Leonardboeker/Hardware_III/.planning/PROJECT.md

# Hardware III — Guided Comparative Assembly

**Subtitle:** An interactive construction kitchen — configure, build, compare.
**Proposal submitted:** April 17, 2026 (`Group_3_Hardware_III_Proposal.pdf`)

## What This Is

A hands-on exhibit for children, young architects, and decision makers.
The user configures a building (footprint, height, material) using physical ArUco pucks and dials on a table. A projector guides them through 5 construction phases — each with CO₂, cost, labor, and logistics data. Three construction methods can be compared: Masonry, 3D Printed, Prefab. No screens. No buttons.

## Core Value

Turn abstract construction data into embodied knowledge:
you *build* the comparison yourself, piece by piece — the statistics emerge from your own hands.

## Concept

**Flow per model:**
1. Piece highlight projected → where to place next element
2. User places physical piece → camera/Kinect confirms position
3. Data appears projected on/around the piece: CO₂, labor hours, material origin, method explanation
4. Sound layer reinforces the data (industrial noise, time-lapse audio, factory vs. site sounds)
5. Next piece highlighted → repeat until model complete
6. Model summary shown → move to next construction method model

**After all models complete:**
- Full comparison statistics projected across all models simultaneously
- CO₂ totals, labor hours, time, cost — side by side
- Sound transitions to a final ambient layer

**Construction methods to compare (TBD, 2–4 models):**
- Traditional masonry / site-built
- 3D-printed concrete / robotic extrusion
- Modular prefabrication / CLT
- (Strong candidate) Reclaimed / reused brick — near-zero embodied carbon, outperforms 3DP on every metric, sharpens the political argument

## FSM States (locked in proposal)

```
IDLE → METHOD → FOOTPRINT → HEIGHT → MATERIALS → VALIDATED → 5 PHASES → COMPARISON
```

- **IDLE**: No model on pedestal
- **METHOD**: RFID read → construction method selected (Masonry / 3D Printed / Prefab)
- **FOOTPRINT**: User arranges 10 ArUco pucks → footprint + m² calculated
- **HEIGHT**: User rotates ArUco dial (ID 10) → floors selected
- **MATERIALS**: User rotates ArUco dial (ID 11) → material variant selected
- **VALIDATED**: System checks feasibility (e.g. earth 3DP max 1 story) → green/red feedback
- **5 PHASES**: Foundation → Structure → Roof → Openings → Finishing (animated, data per phase)
- **COMPARISON**: All data saved, side-by-side dashboard projected

## Layered State Model (current runtime interpretation)

The project now distinguishes three state layers:

1. **Canonical Content FSM**
   `IDLE -> METHOD -> FOOTPRINT -> HEIGHT -> MATERIALS -> VALIDATED -> PHASE_N -> COMPARISON`
2. **System Wrapper States**
   `CALIBRATION_CHECK`, `ERROR`, `RESET`, `MANUAL_OVERRIDE`
3. **Visual Feedback States**
   `DISCONNECTED`, `PENDING`, `INVALID`, `VALID`, `IDLE_ANIM`, `SUMMARY`, `COMPARISON`

The current TouchDesigner runtime should keep these layers separate.
The visitor-facing journey is the canonical content FSM.
Recovery and setup belong to wrapper states.
Projection feedback belongs to visual states.

## Building Phases (locked)

| Phase | Name |
|---|---|
| 1 | Foundation |
| 2 | Structure / Walls |
| 3 | Roof |
| 4 | Openings (windows/doors) |
| 5 | Finishing |

## Input / Sensing

- **USB Webcam overhead**: detects piece placement position on table surface
- **Kinect** (optional): depth sensing for better 3D object recognition, height
- **ESP32 + proximity sensor**: detects when user leans in / reaches for piece → triggers data layer zoom
- **Physical pieces**: color-coded or marker-tagged parts per construction method

## Output

- **Projection on table surface + model surfaces**: placement guides, data overlays, statistics
- **Sound**: construction method audio per step (concrete mixer, robotic printer hum, timber assembly)
- **Statistics view**: final comparison projected as graphic across full table

## Toolkit

- **TouchDesigner** — primary runtime (FSM, projection mapping, vision pipeline). Replaces Anemone/Firefly per locked decision (see below).
- **OpenCV + ArUco** (Python or TD Script CHOP) — camera intake + marker detection
- **Rhino + Grasshopper** — parametric geometry, building generation per method (no longer carries the FSM)
- **Arduino / ESP32** — RFID pedestal + proximity sensor; OSC over WiFi to TouchDesigner
- USB webcam overhead + top-down video projector

## Context

**Course:** Hardware III seminar, MRAC + MAAI 2025/2026
**Instructors:** Hamid Peiro, Aleksandra (Sasha) Kraeva
**Schedule:** 5 course days + Finals (April 10 – May 22, 2026)
**User background:** Ausstellungsbau (exhibition design) — content must be critical and substantive, not just visually reactive

**Key theoretical reference:** Stefana Parascho, "Cooperative Robotic Assembly" (ETH Diss. 25839)
— assembly sequence as FSM, each intermediate state must be valid → directly maps to guided piece placement

**Reference projects (from S1 review):**
- Gramazio Kohler, Augmented Bricklaying, ETH 2018–20 — direct precedent for AR-guided assembly
- Fologram, Steampunk Pavilion, Tallinn 2019 — guided assembly proven with public
- MIT Tangible Media, inFORM, 2013 — canonical tangible dataviz reference
- EPFL SXL, Corentin Fivet — reuse + embodied carbon as design driver
- Striatus Bridge (ZHA + BRG + ETH, 2021) — 3DP concrete visual reference
- Domestic Data Streamers — participatory physical dataviz

**White space:** No precedent exists for a tabletop interactive LCA comparison installation combining guided assembly + tangible dataviz + LCA at table scale.

## Constraints

- **Timeline:** S1 proposal due April 17 — concept locked, execution starts
- **Tech Stack:** Rhino + Grasshopper mandatory (course toolkit)
- **Output:** Projection on physical surface — no screens
- **Team:** Group project — PM schedule required from S1
- **Data:** CO₂ and labor hour data must be sourced/researched for each construction method
- **Models:** Physical replica parts must be fabricated (3D print or laser cut) before Session 4

## Key Decisions

| Decision | Rationale | Outcome |
|---|---|---|
| Comparative structure (2–4 models) | Makes data tangible through contrast | — Pending |
| Guided assembly (not free exploration) | Matches course requirement: FSM + human-in-the-loop | — Pending |
| Table projection (top-down) | Easier calibration, direct piece-to-data feedback | — Pending |
| ArUco fiducial markers on pieces | Color detection unreliable under projector light | — Pending (recommended over color) |
| Sound as equal layer to visuals | Ausstellungsbau background — content depth matters | — Pending |
| Runtime: TouchDesigner vs GH/Anemone | GH is single-threaded; Anemone stalls canvas; webcam under projector light is fragile — TD does projection mapping + CV natively | **LOCKED 2026-05-03 — TouchDesigner** (lit-review strand 03) |
| Build all 3 methods physically vs. 1 physical + 2 animated | 3 full builds = visitor fatigue risk | **LOCKED 2026-05-03 — projected animations**, AI-generated animations paused until LCA numbers sourced |
| LCA data as ranges (with sources) vs. single figures | Single EPD figures vary wildly and collapse under expert questioning | **LOCKED 2026-05-03 — ranges + tier-annotated sources** + methodology-wobble overlay as first-class layer |
| Closed-loop CV vs open-loop button-advance | Closed-loop is the project's novelty contribution; open-loop is a v1 baseline | **LOCKED 2026-05-03 — closed-loop from day one**, manual-override hotkey as emergency demo insurance only |
| Reclaimed brick: 4th competitor vs baseline toggle | A reuse-vs-new bake-off is foregone-conclusion theater | **LOCKED 2026-05-03 — baseline toggle**, frames every other method against it |

## Open Critiques (from S1 peer review — address in proposal)

1. Three full builds may exhaust visitors — consider 1 physical + 2 projected animations
2. LCA numbers must be ranges with cited sources, not single figures
3. Labor-hours mapping is symbolic, not embodied — own that framing explicitly
4. Missing political dimension: who loses jobs in each method?
5. Reused/reclaimed brick as a 4th method is the strongest narrative upgrade available

See `.planning/REVIEW-S1.md` for full critique, additions, and references.

---

## Locked decisions (2026-05-03)

These five positions are taken — backed by the literature review at `docs/research/lit-review/`. They supersede any earlier "Open" entries above. Cited rationale lives in `docs/research/lit-review/ACTIONS.md`.

1. **Closed-loop computer vision from day one.** Every FSM transition is gated by camera confirmation against a projected target.
2. **TouchDesigner is the runtime.** Replaces Anemone (FSM) and Firefly (vision intake) from the original toolkit.
3. **Reclaimed brick is a baseline toggle**, not a 4th competitor.
4. **Methodology-wobble is a first-class projection layer**, not a footnote.
5. **AI-generated phase animations paused** until tier-1 LCA numbers are sourced (Catalonia: CYPE / BEDEC / ITeC / EPDs).

---
*Last updated: 2026-05-03 — toolkit + key decisions realigned to lit-review-backed locked positions*
