Leonardboeker/Hardware_III/.planning/phases/02.1-height-slider/02.1-01-firmware-slider-adc-PLAN.md

---
phase: 02.1-height-slider
plan: 01
type: execute
wave: 1
depends_on: []
files_modified:
  - firmware/esp32-rfid/esp32_rfid/esp32_rfid.ino
autonomous: false
requirements:
  - INP-03
must_haves:
  truths:
    - "ESP32 reads slider on GPIO34 every ~50 ms"
    - "Slider value is median-then-EMA smoothed before quantization"
    - "Firmware emits `FLOOR:<int>` on quantized floor change"
    - "Firmware emits `SLIDER:<0.xxx>` periodically (~200 ms) as alive/debug tick"
    - "Floor boundary hysteresis prevents oscillation"
    - "Existing `RFID:` / `HB:` / `BOOT:` line formats and RC522 SPI pins remain unbroken"
  artifacts:
    - path: "firmware/esp32-rfid/esp32_rfid/esp32_rfid.ino"
      provides: "ESP32 RFID + Slider firmware (single sketch)"
      contains: "constexpr uint8_t SLIDER_PIN = 34"
    - path: "firmware/esp32-rfid/esp32_rfid/esp32_rfid.ino"
      provides: "FLOOR/SLIDER Serial emission"
      contains: "Serial.printf"
  key_links:
    - from: "esp32_rfid.ino loop()"
      to: "analogReadMilliVolts(SLIDER_PIN)"
      via: "ADC sample every ~50 ms"
      pattern: "analogReadMilliVolts\\(SLIDER_PIN\\)"
    - from: "esp32_rfid.ino loop()"
      to: "Serial output"
      via: "FLOOR:/SLIDER: printf"
      pattern: "FLOOR:|SLIDER:"
---

<objective>
Extend the existing ESP32-RFID sketch so it ALSO reads a DollaTek 10K linear-slide potentiometer on GPIO34, smooths it (median FIRST, EMA SECOND), quantizes to a floor index with boundary hysteresis, and emits `FLOOR:<int>` (on change) + `SLIDER:<0.xxx>` (periodic) over USB Serial @115200 — alongside the unchanged `RFID:<HEX>`, `HB:<sec>`, `BOOT:rfid_reader_ready` lines.

Purpose: HEIGHT FSM state needs a physical input. The DollaTek slider replaces ArUco-Dial ID-10 (per ROADMAP Phase 02.1 + CONTEXT.md decision D-Hardware). This is the ONLY firmware change in Phase 02.1; nothing else in the sketch (RFID logic, heartbeat cadence, SPI pins) may shift.
Output: A single rewritten `esp32_rfid.ino` that, when flashed and opened in a Serial Monitor @115200, shows the existing `BOOT:` + `HB:N` + (on tag scan) `RFID:<HEX>` lines PLUS new `FLOOR:N` (only when floor changes) and `SLIDER:0.xxx` (every ~200 ms) lines.
</objective>

<execution_context>
@~/.claude/get-shit-done/workflows/execute-plan.md
@~/.claude/get-shit-done/templates/summary.md
</execution_context>

<context>
@.planning/STATE.md
@.planning/ROADMAP.md
@.planning/phases/02.1-height-slider/02.1-CONTEXT.md
@firmware/esp32-rfid/esp32_rfid/esp32_rfid.ino
@firmware/esp32-rfid/README.md

<interfaces>
<!-- Current Serial line shapes that MUST keep working unchanged. -->
<!-- Existing format (from esp32_rfid.ino lines 37, 46-48, 61-62): -->

BOOT:rfid_reader_ready          // one-shot at boot, line 37
HB:<seconds-since-boot>         // every 1000 ms, lines 46-48
RFID:<UPPERCASE-HEX-UID>        // on new tag (debounced REREAD_MS=1500), lines 61-62

<!-- New line shapes this plan introduces: -->

FLOOR:<int>                     // emitted only on quantized floor change, 1..MAX_FLOORS
SLIDER:<0.xxx>                  // emitted every ~200 ms (3 decimals), smoothed normalized value

<!-- Existing pin reservations that MUST NOT collide with SLIDER_PIN=34: -->

SS_PIN  = 5     // RC522 SDA/SS  (line 21)
SCK     = 18    // SPI clock
MOSI    = 23
MISO    = 19
RST_PIN = 27    // RC522 RST     (line 22)

<!-- GPIO34 is input-only on ESP32, ADC1_CH6 (WiFi-safe). Confirmed by CONTEXT.md. -->
</interfaces>
</context>

<tasks>

<task type="auto" tdd="false">
  <name>Task 1: Add slider constants, ring buffer, EMA state, and helper functions at the top of esp32_rfid.ino</name>
  <files>firmware/esp32-rfid/esp32_rfid/esp32_rfid.ino</files>
  <read_first>
    - firmware/esp32-rfid/esp32_rfid/esp32_rfid.ino (current sketch — see existing constexpr block lines 21-22 and the include block lines 18-19)
    - .planning/phases/02.1-height-slider/02.1-CONTEXT.md (locked decisions block — verbatim values below)
  </read_first>
  <action>
    Edit `firmware/esp32-rfid/esp32_rfid/esp32_rfid.ino`.

    1. After line 19 (`#include <MFRC522.h>`), add `#include <algorithm>` so `std::nth_element` is available for the median.

    2. After the existing RC522 constexpr block (currently lines 21-22 `SS_PIN`/`RST_PIN`), add a new constexpr block for the slider — keep grouping tight so wiring/docs match. Insert verbatim:

       ```cpp
       // ---- Slider (DollaTek 10K linear-slide potentiometer) ----
       // GPIO34 is input-only on ESP32, ADC1_CH6, WiFi-safe.
       constexpr uint8_t  SLIDER_PIN          = 34;
       constexpr uint8_t  MAX_FLOORS          = 5;        // upper bound; per-method caps live TD-side
       constexpr uint8_t  MEDIAN_WINDOW       = 8;        // ring buffer size (CONTEXT.md: median FIRST)
       constexpr float    EMA_ALPHA           = 0.2f;     // tune in jitter test (CONTEXT.md starting point)
       constexpr float    HYST_EPSILON        = 0.02f;    // CONTEXT.md hysteresis nudge
       constexpr unsigned long SLIDER_POLL_MS = 50;       // ADC sample cadence
       constexpr unsigned long SLIDER_EMIT_MS = 200;      // SLIDER:0.xxx periodic emit
       constexpr float    SLIDER_MV_MAX       = 3300.0f;  // ADC_11db: full range ~0..3300 mV
       ```

    3. After the global `lastUid`/`lastReadMs` declarations (currently around lines 29-30), add slider state globals (no `static` inside `loop()` — easier to inspect):

       ```cpp
       // ---- Slider state ----
       uint16_t sliderBuf[MEDIAN_WINDOW] = {0};
       uint8_t  sliderBufCount           = 0;          // grows to MEDIAN_WINDOW then stays
       uint8_t  sliderBufHead            = 0;          // circular write index
       float    sliderEma                = 0.0f;       // last smoothed normalized value [0, 1]
       uint8_t  lastFloor                = 1;          // 1..MAX_FLOORS
       float    lastFloorCenter          = 0.0f;       // normalized centre of lastFloor (for hysteresis)
       unsigned long lastSliderPollMs    = 0;
       unsigned long lastSliderEmitMs    = 0;
       ```

    4. Above `void setup()` (insert before the `void setup()` line), add two helper functions verbatim:

       ```cpp
       // Floor centre for a given 1..MAX_FLOORS index, in normalized [0, 1] space.
       static inline float floorCenter(uint8_t f) {
         if (MAX_FLOORS <= 1) return 0.0f;
         return (float)(f - 1) / (float)(MAX_FLOORS - 1);
       }

       // Quantize a normalized [0, 1] value to a floor 1..MAX_FLOORS.
       static inline uint8_t quantizeFloor(float norm) {
         if (norm < 0.0f) norm = 0.0f;
         if (norm > 1.0f) norm = 1.0f;
         float f = 1.0f + norm * (float)(MAX_FLOORS - 1);
         long  r = lroundf(f);
         if (r < 1) r = 1;
         if (r > (long)MAX_FLOORS) r = MAX_FLOORS;
         return (uint8_t)r;
       }

       // Median of the live samples in sliderBuf (only the first sliderBufCount entries are valid).
       static inline uint16_t sliderMedian() {
         uint16_t copy[MEDIAN_WINDOW];
         uint8_t  n = sliderBufCount;
         if (n == 0) return 0;
         for (uint8_t i = 0; i < n; i++) copy[i] = sliderBuf[i];
         std::nth_element(copy, copy + n / 2, copy + n);
         return copy[n / 2];
       }
       ```

    Do NOT touch the existing `MFRC522 rfid(SS_PIN, RST_PIN)` declaration, the `REREAD_MS` constant, `lastUid`, `lastReadMs`, or any line below `void setup()` in this task.
  </action>
  <verify>
    <automated>powershell -NoProfile -Command "$f='firmware/esp32-rfid/esp32_rfid/esp32_rfid.ino'; $c=Get-Content -Raw $f; if (-not ($c -match 'constexpr uint8_t\s+SLIDER_PIN\s*=\s*34')) { throw 'SLIDER_PIN missing' }; if (-not ($c -match 'constexpr uint8_t\s+MAX_FLOORS\s*=\s*5')) { throw 'MAX_FLOORS missing' }; if (-not ($c -match 'constexpr uint8_t\s+MEDIAN_WINDOW\s*=\s*8')) { throw 'MEDIAN_WINDOW missing' }; if (-not ($c -match 'constexpr float\s+EMA_ALPHA\s*=\s*0\.2f')) { throw 'EMA_ALPHA missing' }; if (-not ($c -match 'constexpr float\s+HYST_EPSILON\s*=\s*0\.02f')) { throw 'HYST_EPSILON missing' }; if (-not ($c -match '#include <algorithm>')) { throw 'algorithm include missing' }; if (-not ($c -match 'sliderMedian')) { throw 'sliderMedian helper missing' }; if (-not ($c -match 'quantizeFloor')) { throw 'quantizeFloor helper missing' }; if (-not ($c -match 'floorCenter')) { throw 'floorCenter helper missing' }; Write-Host 'OK'"</automated>
  </verify>
  <acceptance_criteria>
    - File `firmware/esp32-rfid/esp32_rfid/esp32_rfid.ino` exists.
    - `grep -c "constexpr uint8_t SLIDER_PIN = 34" esp32_rfid.ino` >= 1.
    - `grep -c "constexpr uint8_t MAX_FLOORS = 5" esp32_rfid.ino` >= 1.
    - `grep -c "constexpr uint8_t MEDIAN_WINDOW = 8" esp32_rfid.ino` >= 1.
    - `grep -c "constexpr float EMA_ALPHA = 0.2f" esp32_rfid.ino` >= 1.
    - `grep -c "constexpr float HYST_EPSILON = 0.02f" esp32_rfid.ino` >= 1.
    - `grep -c "#include <algorithm>" esp32_rfid.ino` >= 1.
    - `grep -c "static inline uint8_t quantizeFloor" esp32_rfid.ino` >= 1.
    - `grep -c "static inline uint16_t sliderMedian" esp32_rfid.ino` >= 1.
    - `grep -c "static inline float floorCenter" esp32_rfid.ino` >= 1.
    - `grep -c "constexpr uint8_t SS_PIN" esp32_rfid.ino` == 1 (existing line untouched).
    - `grep -c "constexpr uint8_t RST_PIN" esp32_rfid.ino` == 1 (existing line untouched).
    - `grep -c "MFRC522 rfid(SS_PIN, RST_PIN)" esp32_rfid.ino` == 1 (existing declaration untouched).
  </acceptance_criteria>
  <done>Slider constants, state globals, and helper functions exist at the top of esp32_rfid.ino without disturbing RC522 declarations.</done>
</task>

<task type="auto" tdd="false">
  <name>Task 2: Add slider sample loop, smoothing, hysteresis, and FLOOR/SLIDER Serial emission inside loop()</name>
  <files>firmware/esp32-rfid/esp32_rfid/esp32_rfid.ino</files>
  <read_first>
    - firmware/esp32-rfid/esp32_rfid/esp32_rfid.ino (after Task 1 — slider constants and helpers must be present)
    - .planning/phases/02.1-height-slider/02.1-CONTEXT.md (signal-conditioning + transport blocks)
  </read_first>
  <action>
    Edit `firmware/esp32-rfid/esp32_rfid/esp32_rfid.ino`.

    1. Inside `void setup()` (currently lines 32-38), add the ADC attenuation configuration AFTER `Serial.begin(115200)` but BEFORE `SPI.begin()`. Insert verbatim (use `analogSetPinAttenuation` from the ESP32 core — works on Arduino-ESP32 >= 2.0):

       ```cpp
         // Slider ADC: 0..3.3 V full range
         analogSetPinAttenuation(SLIDER_PIN, ADC_11db);
         analogReadResolution(12);              // 0..4095 raw if we ever need raw; we use millivolts API
         lastSliderPollMs = millis();
         lastSliderEmitMs = millis();
       ```

       (Place these 4 lines between `Serial.begin(115200);` block and `SPI.begin();`.)

    2. Inside `void loop()`, AFTER the existing heartbeat block (currently lines 42-48 — the `if (now - lastHb >= 1000)` block) and BEFORE the `if (!rfid.PICC_IsNewCardPresent()) return;` line, insert the slider polling block verbatim:

       ```cpp
         // ---- Slider poll (every SLIDER_POLL_MS ms) ----
         if (now - lastSliderPollMs >= SLIDER_POLL_MS) {
           lastSliderPollMs = now;

           // 1) Sample ADC in millivolts (calibrated by ESP32 core).
           uint32_t mv = analogReadMilliVolts(SLIDER_PIN);
           if (mv > (uint32_t)SLIDER_MV_MAX) mv = (uint32_t)SLIDER_MV_MAX;

           // 2) Push into ring buffer.
           sliderBuf[sliderBufHead] = (uint16_t)mv;
           sliderBufHead = (sliderBufHead + 1) % MEDIAN_WINDOW;
           if (sliderBufCount < MEDIAN_WINDOW) sliderBufCount++;

           // 3) Median FIRST (kills single-tick spikes).
           uint16_t med_mv = sliderMedian();
           float    med_norm = (float)med_mv / SLIDER_MV_MAX;
           if (med_norm < 0.0f) med_norm = 0.0f;
           if (med_norm > 1.0f) med_norm = 1.0f;

           // 4) EMA SECOND (smooths the post-median signal).
           //    On the very first valid sample, seed EMA to med_norm so we don't ramp from 0.
           static bool emaSeeded = false;
           if (!emaSeeded) {
             sliderEma = med_norm;
             lastFloor = quantizeFloor(sliderEma);
             lastFloorCenter = floorCenter(lastFloor);
             emaSeeded = true;
           } else {
             sliderEma = (EMA_ALPHA * med_norm) + ((1.0f - EMA_ALPHA) * sliderEma);
           }

           // 5) Hysteresis-gated quantization. Floor only changes when the smoothed value has
           //    moved more than half a floor-step away from the current floor's centre, plus EPSILON.
           const float halfStep = (MAX_FLOORS > 1)
             ? (1.0f / (2.0f * (float)(MAX_FLOORS - 1)))
             : 0.5f;
           if (fabsf(sliderEma - lastFloorCenter) > (halfStep + HYST_EPSILON)) {
             uint8_t newFloor = quantizeFloor(sliderEma);
             if (newFloor != lastFloor) {
               lastFloor = newFloor;
               lastFloorCenter = floorCenter(lastFloor);
               Serial.printf("FLOOR:%u\n", (unsigned)lastFloor);
             }
           }
         }

         // ---- Slider periodic emit (every SLIDER_EMIT_MS ms) ----
         if (now - lastSliderEmitMs >= SLIDER_EMIT_MS) {
           lastSliderEmitMs = now;
           Serial.printf("SLIDER:%.3f\n", sliderEma);
         }
       ```

    Do NOT modify the existing RFID block (`if (!rfid.PICC_IsNewCardPresent())` through `rfid.PCD_StopCrypto1();`), the heartbeat block, or the `REREAD_MS` debounce logic. Both `now` is already declared at the top of `loop()` (currently line 43 `unsigned long now = millis();`) — reuse it; do not redeclare.
  </action>
  <verify>
    <automated>powershell -NoProfile -Command "$f='firmware/esp32-rfid/esp32_rfid/esp32_rfid.ino'; $c=Get-Content -Raw $f; if (-not ($c -match 'analogSetPinAttenuation\(SLIDER_PIN,\s*ADC_11db\)')) { throw 'ADC attenuation missing' }; if (-not ($c -match 'analogReadMilliVolts\(SLIDER_PIN\)')) { throw 'mV read missing' }; if (-not ($c -match 'Serial\.printf\(\"FLOOR:%u')) { throw 'FLOOR emit missing' }; if (-not ($c -match 'Serial\.printf\(\"SLIDER:%\.3f')) { throw 'SLIDER emit missing' }; if (-not ($c -match 'sliderMedian\(\)')) { throw 'median call missing' }; if (-not ($c -match 'EMA_ALPHA \* med_norm')) { throw 'EMA missing' }; if (-not ($c -match 'halfStep \+ HYST_EPSILON')) { throw 'hysteresis missing' }; if (-not ($c -match 'PICC_IsNewCardPresent')) { throw 'RFID code disturbed' }; if (-not ($c -match 'Serial\.print\(\"HB:\"\)')) { throw 'HB emit disturbed' }; if (-not ($c -match 'Serial\.println\(\"BOOT:rfid_reader_ready\"\)')) { throw 'BOOT line disturbed' }; Write-Host 'OK'"</automated>
  </verify>
  <acceptance_criteria>
    - `grep -c "analogSetPinAttenuation(SLIDER_PIN, ADC_11db)" esp32_rfid.ino` >= 1.
    - `grep -c "analogReadMilliVolts(SLIDER_PIN)" esp32_rfid.ino` >= 1.
    - `grep -c 'Serial.printf("FLOOR:%u' esp32_rfid.ino` >= 1.
    - `grep -c 'Serial.printf("SLIDER:%.3f' esp32_rfid.ino` >= 1.
    - `grep -c "sliderMedian()" esp32_rfid.ino` >= 1.
    - `grep -c "EMA_ALPHA \* med_norm" esp32_rfid.ino` >= 1.
    - `grep -c "halfStep + HYST_EPSILON" esp32_rfid.ino` >= 1.
    - `grep -c "PICC_IsNewCardPresent" esp32_rfid.ino` == 1 (RFID code untouched).
    - `grep -c 'Serial.print("HB:")' esp32_rfid.ino` == 1 (HB line untouched).
    - `grep -c 'Serial.println("BOOT:rfid_reader_ready")' esp32_rfid.ino` == 1 (BOOT line untouched).
    - `grep -c "REREAD_MS" esp32_rfid.ino` == 2 (constant declaration + use, both unchanged).
  </acceptance_criteria>
  <done>loop() polls slider every 50 ms with median+EMA+hysteresis, emits FLOOR on quantized change and SLIDER every 200 ms, all existing RFID/heartbeat/boot behaviour intact.</done>
</task>

<task type="checkpoint:human-verify" gate="blocking">
  <name>Task 3: Flash to ESP32 and verify Serial Monitor output (BOOT + HB + FLOOR + SLIDER + RFID all present, no breakage)</name>
  <files>firmware/esp32-rfid/esp32_rfid/esp32_rfid.ino</files>
  <read_first>
    - firmware/esp32-rfid/esp32_rfid/esp32_rfid.ino (post Task 1 + Task 2 — full sketch must be in place)
    - firmware/esp32-rfid/LAB-SETUP-GUIDE.md (lab procedure reference)
    - .planning/phases/02.1-height-slider/02.1-CONTEXT.md (verification path block — the three demo scenarios)
  </read_first>
  <action>
    Human-verify checkpoint. Claude STOPS here and waits for the user to flash the firmware and confirm.

    Procedure for the user (mirrors `<how-to-verify>` below):

    1. Open `firmware/esp32-rfid/esp32_rfid/esp32_rfid.ino` in Arduino IDE 2.x.
    2. Select board: Tools -> Board -> ESP32 Arduino -> ESP32 Dev Module.
    3. Select port: Tools -> Port -> the COM port the ESP32 enumerates as.
    4. Wire the DollaTek slider exactly: VCC -> ESP32 3V3, GND -> ESP32 GND, wiper -> ESP32 GPIO34 (CONTEXT.md Hardware block).
    5. Sketch -> Upload (hold BOOT button on the ESP32 if you see `Failed to connect`).
    6. Tools -> Serial Monitor, baud 115200.
    7. Observe expected output and exercise slider sweep, boundary hold, and RFID scan as described in `<how-to-verify>`.
    8. Type the resume signal (`approved` or a failure description).
  </action>
  <what-built>
    Updated `esp32_rfid.ino` reads DollaTek slider on GPIO34, prints `FLOOR:N` on quantized change and `SLIDER:0.xxx` every ~200 ms, alongside untouched `BOOT:rfid_reader_ready`, `HB:N`, and `RFID:<HEX>` lines.
  </what-built>
  <how-to-verify>
    1. Open `firmware/esp32-rfid/esp32_rfid/esp32_rfid.ino` in Arduino IDE 2.x.
    2. Board: ESP32 Dev Module. Port: the COM port the ESP32 enumerates as.
    3. Wire the DollaTek slider: VCC -> ESP32 3V3, GND -> ESP32 GND, wiper -> ESP32 GPIO34 (CONTEXT.md Hardware block, mirrored in Plan 03 docs).
    4. Verify -> Upload (hold BOOT button if `Failed to connect`).
    5. Tools -> Serial Monitor, baud 115200. Expected within 2 seconds of reset:
       ```
       BOOT:rfid_reader_ready
       SLIDER:0.xxx
       HB:1
       SLIDER:0.xxx
       SLIDER:0.xxx
       SLIDER:0.xxx
       SLIDER:0.xxx
       HB:2
       ...
       ```
    6. Slowly drag the slider from one end to the other. Expected: `FLOOR:1` -> `FLOOR:2` -> ... -> `FLOOR:5` interleaved between SLIDER ticks. Total quantized steps observed should be `MAX_FLOORS = 5`.
    7. Park slider at a known boundary (e.g. the transition between FLOOR:2 and FLOOR:3) and hold for >=5 s. Expected: NO FLOOR line emitted while parked (hysteresis works).
    8. Tap an RFID tag on the RC522 (any registered or unregistered tag). Expected: `RFID:<HEX>` line appears between SLIDER/HB ticks. This proves the slider polling did NOT break SPI/RFID timing.
    9. Confirm exactly ONE `HB:N` per second (heartbeat unchanged).
  </how-to-verify>
  <verify>
    Human verification (no automated command — this is a hardware-in-loop check). The user runs the procedure in `<how-to-verify>` and confirms each of the 5 observable behaviors.
  </verify>
  <acceptance_criteria>
    - User confirms `BOOT:rfid_reader_ready` appears once at reset.
    - User confirms `HB:N` appears exactly once per second (heartbeat cadence unchanged).
    - User confirms `SLIDER:0.xxx` appears every ~200 ms continuously.
    - User confirms `FLOOR:1` through `FLOOR:5` all appear during a single sweep (5 quantized steps).
    - User confirms holding slider at a floor boundary for >=5 s produces NO additional `FLOOR:` line (hysteresis works).
    - User confirms tapping an RFID tag produces a `RFID:<HEX>` line (RFID path intact).
  </acceptance_criteria>
  <done>User types `approved` (all 5 behaviors observed) OR provides a failure description that will become a gap-closure input for Plan 02.1-01.</done>
  <resume-signal>Type "approved" if all 5 expected behaviors (BOOT/HB/SLIDER ticks/FLOOR transitions across 5 quantized steps/no boundary jitter/RFID still works) are observed. Otherwise describe what failed.</resume-signal>
</task>

</tasks>

<verification>
- Sketch compiles cleanly in Arduino IDE 2.x with ESP32 Dev Module board selected (no MFRC522 library breakage).
- Serial Monitor @115200 shows BOOT + HB + SLIDER + FLOOR + RFID lines, all four pre-existing line shapes intact.
- Slider sweep produces 5 distinct floors (1..5) without boundary oscillation.
- RFID tag scan still emits `RFID:<HEX>` despite added slider polling load.
</verification>

<success_criteria>
- ROADMAP Phase 02.1 success criterion #1 satisfied: ESP32-RFID firmware reads slider ADC (GPIO34), applies median + EMA + hysteresis, emits FLOOR:N on change and SLIDER:0.xxx periodically.
- No regression on existing RFID/HB/BOOT lines.
</success_criteria>

<output>
After completion, create `.planning/phases/02.1-height-slider/02.1-01-SUMMARY.md` per the standard template, documenting: pin choice (GPIO34), sample cadence (50 ms / 200 ms), median window (8), EMA alpha (0.2), hysteresis epsilon (0.02), and any deviations chosen during the jitter test (alpha/window tuning).
</output>
