Leonardboeker/Hardware_III/docs/research/lit-review/06-comparative-lca-and-museum-interactives.md

# 06 — Comparative LCA and Museum Sustainability Interactives

## Scope

This review covers two interlinked bodies of literature that the IAAC tabletop installation depends on:

1. **Comparative LCA studies** for housing built with traditional masonry, 3D-printed concrete or earth, and modular prefab — the actual numbers that need to appear on the projector.
2. **Museum and science-center precedents** for interactive sustainability and construction exhibits — what works pedagogically and what gets evaluated as effective.

The review is deliberately conservative: every per-m² number is tagged with its source tier (peer-reviewed, EPD/database, or grey/marketing) so the team knows which figures are defensible to a jury and which are illustrative only.

## Search strategy

WebSearch + WebFetch on Journal of Cleaner Production, Building & Environment, Energy & Buildings, ScienceDirect, MDPI, Springer, Nature Scientific Reports for LCA; ITeC and BEDEC for the Catalan baseline; institutional sites for Climate Museum, Triennale, Vitra, Cooper Hewitt, mudac, Disseny Hub, Eden Project, California Academy of Sciences, Ars Electronica; Routledge / Wiley / SEGD for visitor-studies literature (Falk & Dierking, Allen). Searches were run May 2026. Marketing claims by 3DCP vendors (ICON, Apis Cor, COBOD) are flagged where used and never substituted for peer-reviewed numbers.

---

## Part A: Comparative LCA for housing construction methods

### Key works (annotated)

### Mohammad et al. (2023) — *A systematic review of life cycle assessments of 3D concrete printing*, Cleaner Materials (ScienceDirect)
Synthesises ~30 LCA studies of 3DCP. Headline conclusion: claims of carbon savings are highly sensitive to (a) the cement content of the printable mix, (b) whether reinforcement is included in the boundary, and (c) the comparative baseline. Many studies omit rebar or steel mesh, which artificially favours 3DCP. URL: https://www.sciencedirect.com/science/article/pii/S2666412723000132

### Alhumayani et al. (2020) — *Environmental assessment of large-scale 3D printing in construction: A comparative study between cob and concrete*, Journal of Cleaner Production
Frequently cited comparison of 3D-printed cob (earth) vs printed concrete vs conventional masonry walls. Cob walls reduced GWP by ~80% vs printed concrete. Important caveat: thermal performance and lifespan of cob assumed equivalent, which is contestable.

### Kuzmenko et al. (2020) / Bhattacherjee et al. (2024) — *3D Concrete Printing Sustainability: A Comparative Life Cycle Assessment of Four Construction Method Scenarios*, Buildings 10(12), 245 (MDPI)
One of the cleanest four-way comparisons (cast in situ, precast, 3DCP wall, 3DCP optimised wall). Found 3DCP advantage only when geometry optimisation reduces material volume — straight printed walls underperform conventional. URL: https://www.mdpi.com/2075-5309/10/12/245

### Findings (2024) — *Comparison of Embodied Carbon of 3D-printed vs. Conventionally Built Houses*
Reports averages of **58 kg CO₂-eq/m² for 3D-printed houses vs 147 kg CO₂-eq/m² for conventional houses**. The factor-of-2 gap is unusually large and the authors attribute it to material quantity reduction; should be treated as upper-bound benefit. URL: https://findingspress.org/article/89707

### Recent ScienceDirect study (2026) — *On the sustainability of digital construction: Whole building life cycle carbon emissions according to three construction techniques*
Models 3DPC vs stick-frame (STF) vs concrete masonry unit (CMU) across four U.S. climate zones, 75- and 100-year service lives. Over 100 years, embodied carbon of 3DPC homes is **10% lower than CMU and 5% lower than STF**, with operational savings of 2–13% depending on climate. The most defensible recent number — modest, not revolutionary. URL: https://www.sciencedirect.com/science/article/abs/pii/S2352710226004845

### Younis et al. / Liu et al. (2021) — *Comparative life cycle assessment of cross laminated timber building and concrete building with special focus on biogenic carbon*, Energy & Buildings
Found CLT building had lower impact in 11 of 18 LCA categories. Embodied GHG of CLT reduced by **46.5% in production+construction stage** vs concrete equivalent; primary energy reduced 32.5%. Biogenic carbon accounting drives much of the gap — strip it out and savings shrink to ~20–30%. URL: https://www.sciencedirect.com/science/article/pii/S0378778821008884

### Hemmati et al. (2024) — *Comparison of Embodied Carbon Footprint of a Mass Timber Building*, USDA Forest Products Lab / Buildings
Mass timber building: **198 kg CO₂-eq/m²** vs steel **243 kg CO₂-eq/m²**. Mass timber alternative achieves ~48 kg CO₂-eq/m² lower mean embodied carbon vs concrete counterpart. URL: https://www.fpl.fs.usda.gov/documnts/pdf2024/fpl_2024_hemmati002.pdf

### Wang et al. (2024) — *Comparative analysis of embodied carbon in modular and conventional construction methods in Hong Kong*, Scientific Reports 14
High-rise concrete modular (MiC) shows ~6% GWP reduction vs site-built initially, rising to **20–26% lower annual emissions** when modules are reused over a 25–50 year second life. Reuse — not prefabrication itself — is the carbon lever. URL: https://www.nature.com/articles/s41598-024-73906-7

### Pomponi & Moncaster (2016, 2017) — *Scrutinising embodied carbon in buildings: The next performance gap made manifest*, Journal of Cleaner Production
The methodological backbone. Documents that LCA results for nominally identical buildings vary by factors of 2–4 due to system boundary choices, biogenic carbon treatment, transport assumptions, and end-of-life scenarios. Required reading before any number is put on a public projector. URL: https://www.sciencedirect.com/science/article/abs/pii/S136403211730998X

### De Wolf, Hertwich et al. (2023) — *Reducing embodied carbon in structural systems: A review of early-stage design strategies*, MIT preprint
Current consensus on mitigation hierarchy. Reinforces Pomponi's caution: comparative claims must be on units of structural performance, not mass. URL: https://dspace.mit.edu/bitstream/handle/1721.1/152266/2023-06-09%20preprint.pdf

### TECLA (Mario Cucinella Architects + WASP, 2021) — *3D-printed earth house, Massa Lombarda*
Built precedent, **not** a peer-reviewed LCA. 60 m² shell, 200 hours print time, ~6 kW average draw (~1200 kWh total printing energy), zero-waste local-soil mix. Useful as a vendor case study and image source; do **not** quote a per-m² CO₂ figure from project PR. URL: https://www.3dwasp.com/en/3d-printed-house-tecla/

### DFAB House (NCCR Digital Fabrication / ETH Zurich, 2019)
Digitally planned and robotically built demonstrator on the NEST building (Empa). Demonstrates Mesh Mould, Smart Slab, Smart Dynamic Casting, Spatial Timber Assemblies. Long-term monitoring is published in NCCR reports; stand-alone full-LCA papers per element exist (e.g., Smart Slab embodied-carbon comparisons claim ~70% material reduction in slab) but should be cited per element, not per house. [unverified for whole-house LCA] URL: https://dfab.ch/ktt-projects/dfab-house

### Banco BEDEC / ITeC (Catalonia, updated 2025–2026)
The defensible Catalan/Spanish baseline. Contains environmental indicators (CO₂, manufacturing energy, waste, recycled content) for ~800,000 construction items aligned with EN 15804:2012+A2:2020. The 2026 release expanded to 22 environmental indicators. **This is what the team should quote for masonry numbers in a Barcelona context** rather than UK/US averages. URL: https://en.itec.cat/services/bedec/

### Headline numbers the team can use (with sources)

The team should present these as ranges, not point values, and always cite. Numbers below are cradle-to-gate (A1–A3) per m² of gross floor area unless noted.

| Method | Embodied carbon (kg CO₂-eq / m² GFA) | Source tier | Citation |
|---|---|---|---|
| Conventional residential (general benchmark) | 150–210 | Peer-reviewed range | RMI / ScienceDirect synthesis |
| Concrete masonry unit (CMU) house, US | ~165 (baseline in 3DPC comparison) | Peer-reviewed | ScienceDirect 2026 study |
| Brick / stabilised laterite housing (Ghana case) | 268 | Peer-reviewed (regional) | PubMed 39995940 |
| Reinforced-concrete residential | ~200–250 | Peer-reviewed range | Hemmati 2024; Liu 2021 |
| 3D-printed concrete house (modest claim) | 5–10% below CMU/STF baseline | Peer-reviewed | ScienceDirect 2026 |
| 3D-printed concrete house (optimistic claim) | 58 vs 147 (factor of ~2.5) | Peer-reviewed but contested | Findings 2024 |
| 3D-printed earth (cob) wall element | ~80% reduction vs printed concrete (wall only) | Peer-reviewed | Alhumayani 2020 |
| Mass timber / CLT building | ~150–200 (often cited 198) | Peer-reviewed | Hemmati 2024 |
| CLT vs concrete (apartment, biogenic in) | 30–46% lower GHG | Peer-reviewed | Liu 2021 |
| Concrete modular (volumetric) initial build | ~6% lower than site-built | Peer-reviewed | Wang 2024 (Sci Reports) |
| Concrete modular with reuse | 20–26% lower annual emissions | Peer-reviewed | Wang 2024 |
| Brick (material only) | 0.20 kg CO₂-eq / kg (avg of 0.195–0.271) | EPD-derived | MDPI Energies 2023 |

For the Barcelona context, replace generic numbers with BEDEC line items: BEDEC contains EPD-aligned values for fired clay block, hollow concrete block, and CLT panels supplied to Spanish sites and is the only source a Catalan jury will treat as locally defensible.
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
