Leonardboeker/Hardware_III/docs/research/lit-review/ACTIONS.md

# ACTIONS — Path Forward (derived from the lit review)

**Compiled:** 2026-05-03
**For:** IAAC Hardware III, Group 3
**Final demo:** 2026-05-22 (19 days from compile date)
**Source:** `OVERVIEW.md` and the six per-strand reports (`01`–`06`) in this folder

---

## Locked decisions

These four positions are taken. The rationale lives in the strand files cited next to each.
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
