Leonardboeker/Hardware_III/cad/aruco-markers/aruco_id00_footprint.png

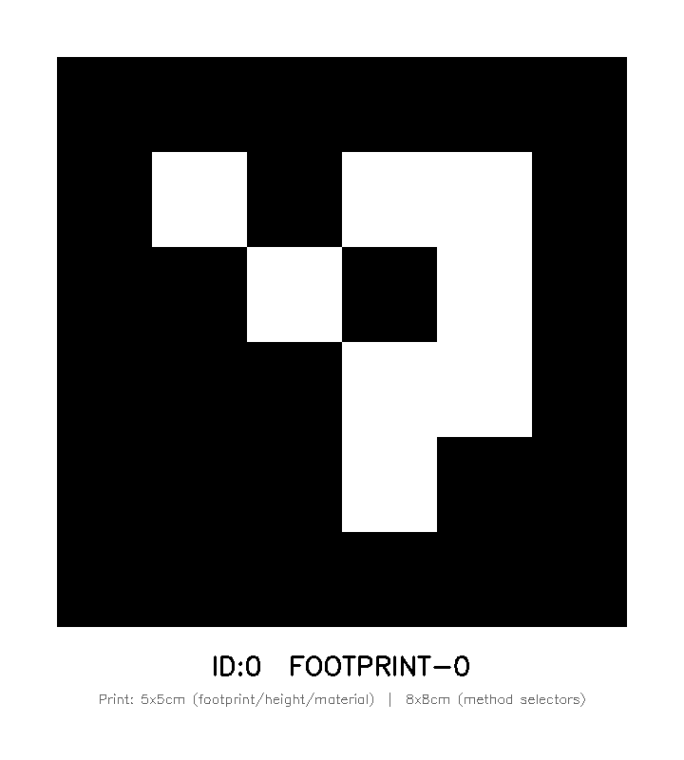
cad/aruco-markers/aruco_id00_footprint.png
