Leonardboeker/Hardware_III/cad/aruco-markers/aruco_id01_footprint.png

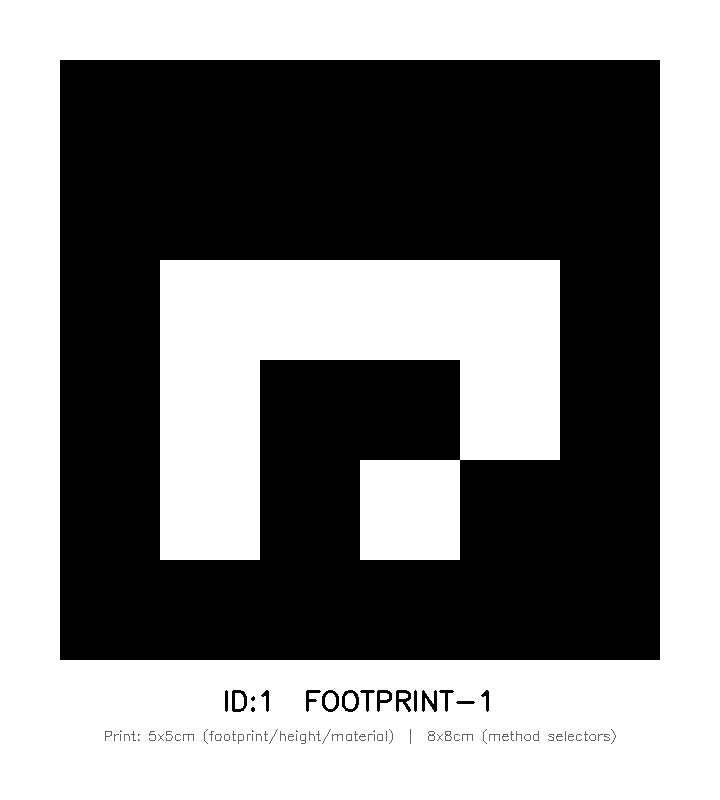
cad/aruco-markers/aruco_id01_footprint.png
