Leonardboeker/Hardware_III/cad/aruco-markers/aruco_id02_footprint.png

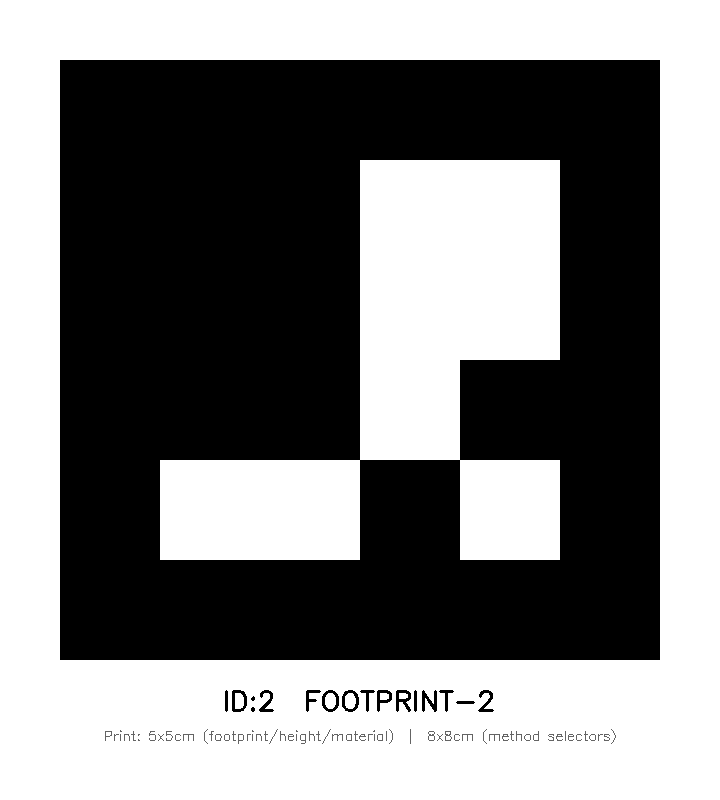
cad/aruco-markers/aruco_id02_footprint.png
