Leonardboeker/Hardware_III/cad/aruco-markers/aruco_id03_footprint.png

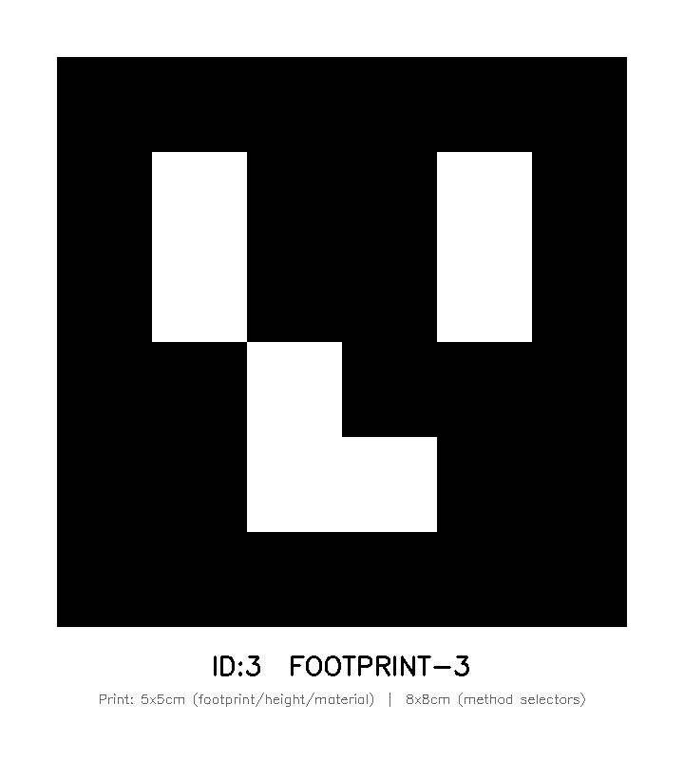
cad/aruco-markers/aruco_id03_footprint.png
