Leonardboeker/Hardware_III/cad/aruco-markers/aruco_id04_footprint.png

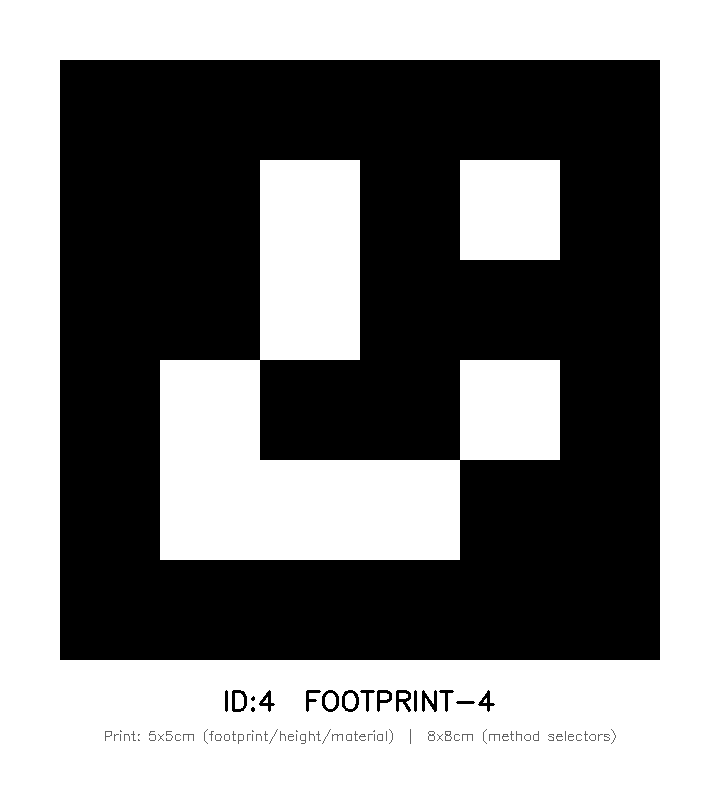
cad/aruco-markers/aruco_id04_footprint.png
