Leonardboeker/Hardware_III/cad/aruco-markers/aruco_id06_footprint.png

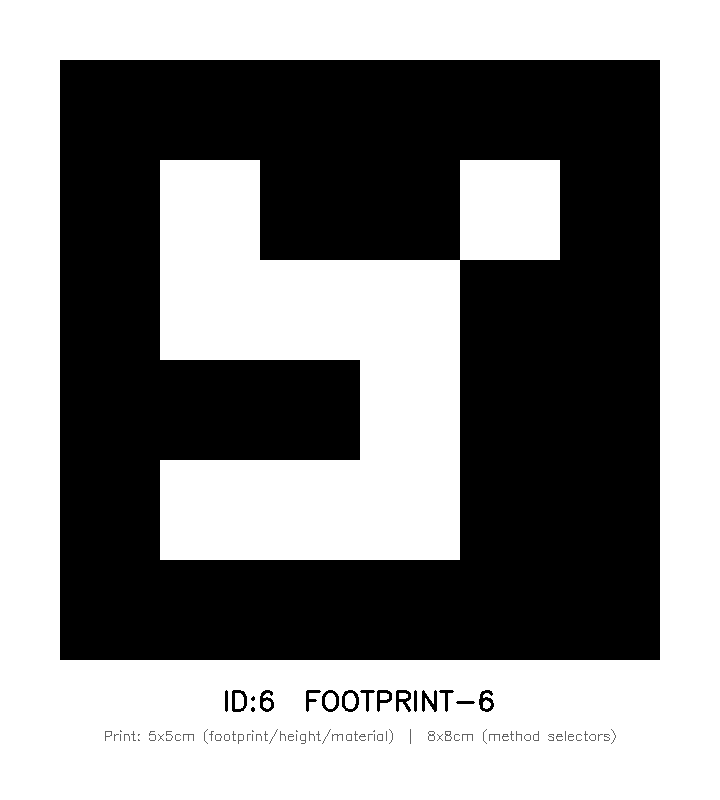
cad/aruco-markers/aruco_id06_footprint.png
