Leonardboeker/Hardware_III/cad/aruco-markers/aruco_id07_footprint.png

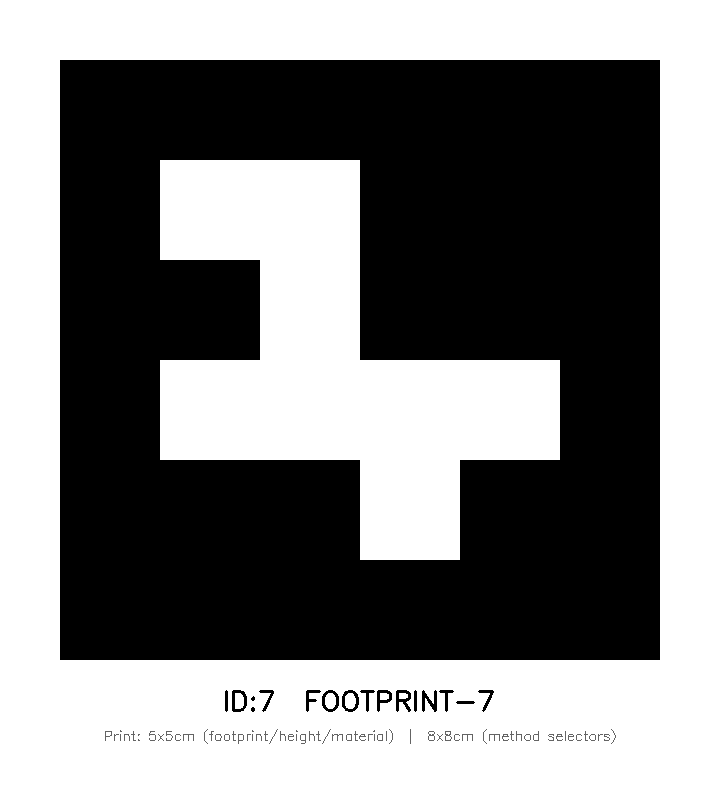
cad/aruco-markers/aruco_id07_footprint.png
