Leonardboeker/Hardware_III/cad/aruco-markers/aruco_id09_footprint.png

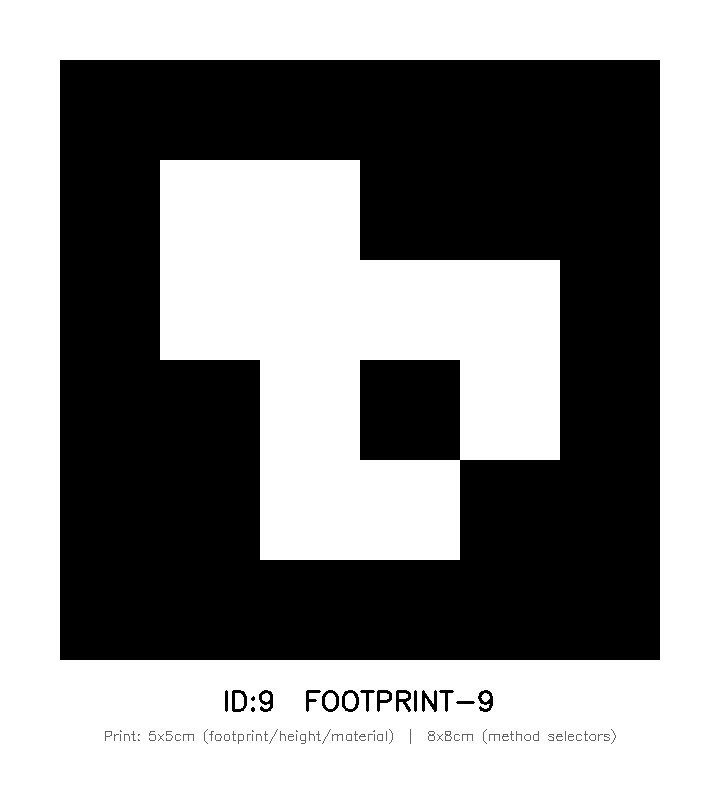
cad/aruco-markers/aruco_id09_footprint.png
