Leonardboeker/Hardware_III/cad/aruco-markers/aruco_id10_height.png

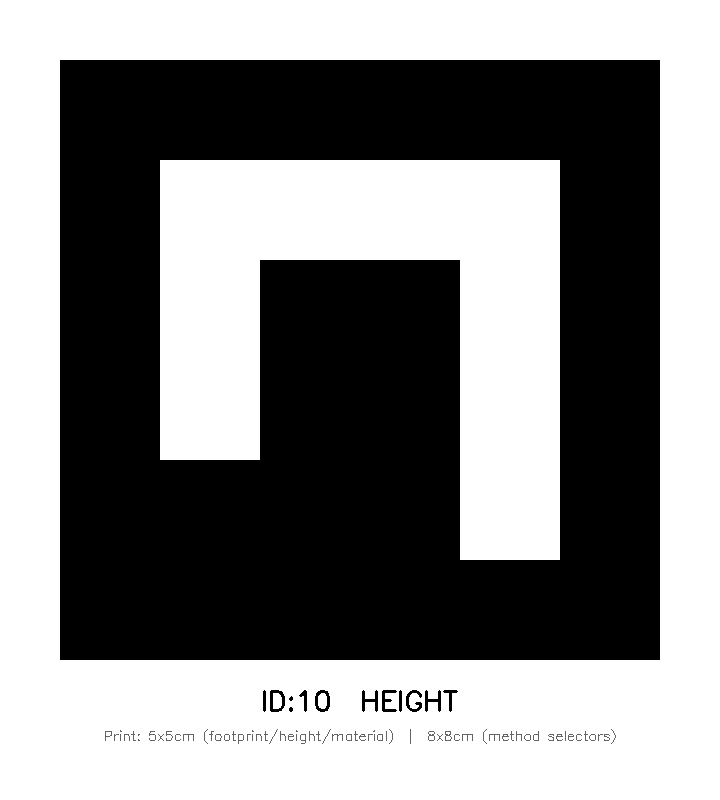
cad/aruco-markers/aruco_id10_height.png
