Leonardboeker/Hardware_III/deliverables/FSM_updated.png

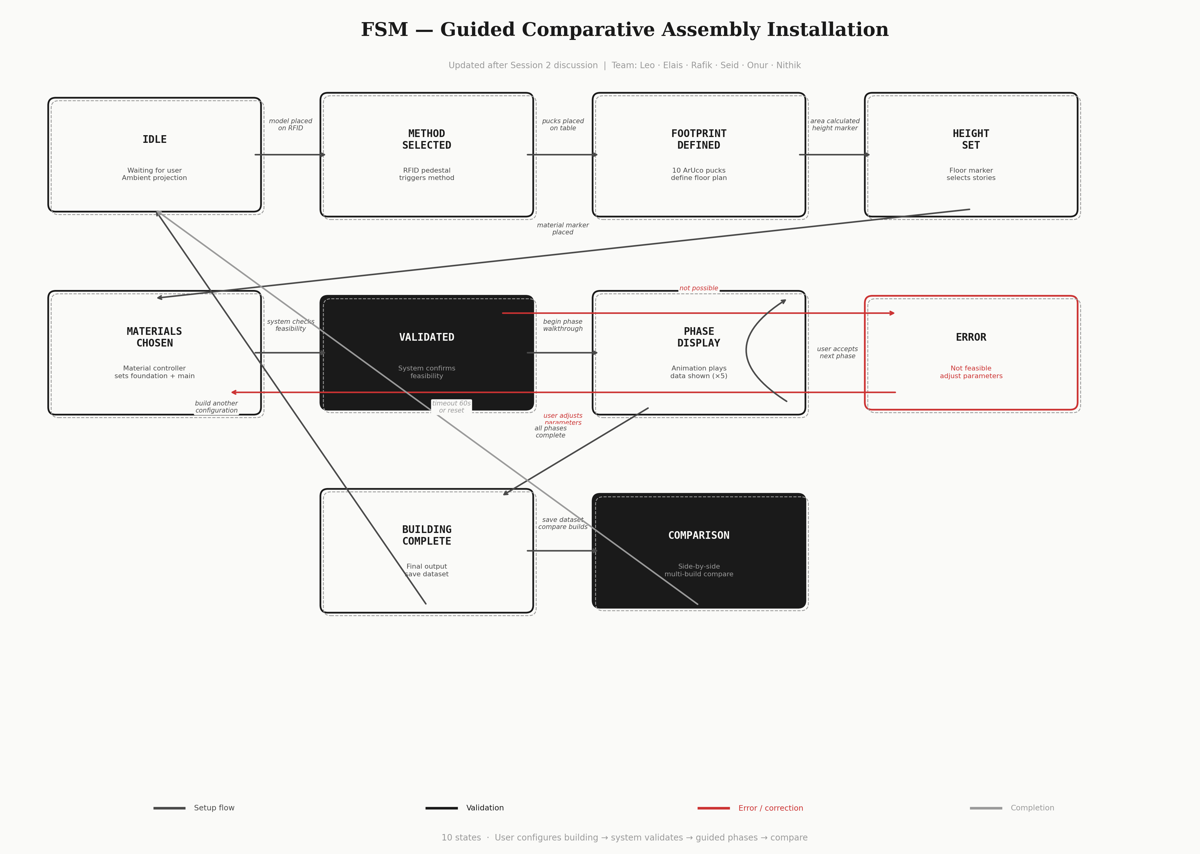
deliverables/FSM_updated.png
