Leonardboeker/Hardware_III/deliverables/screenshot_slide2.png

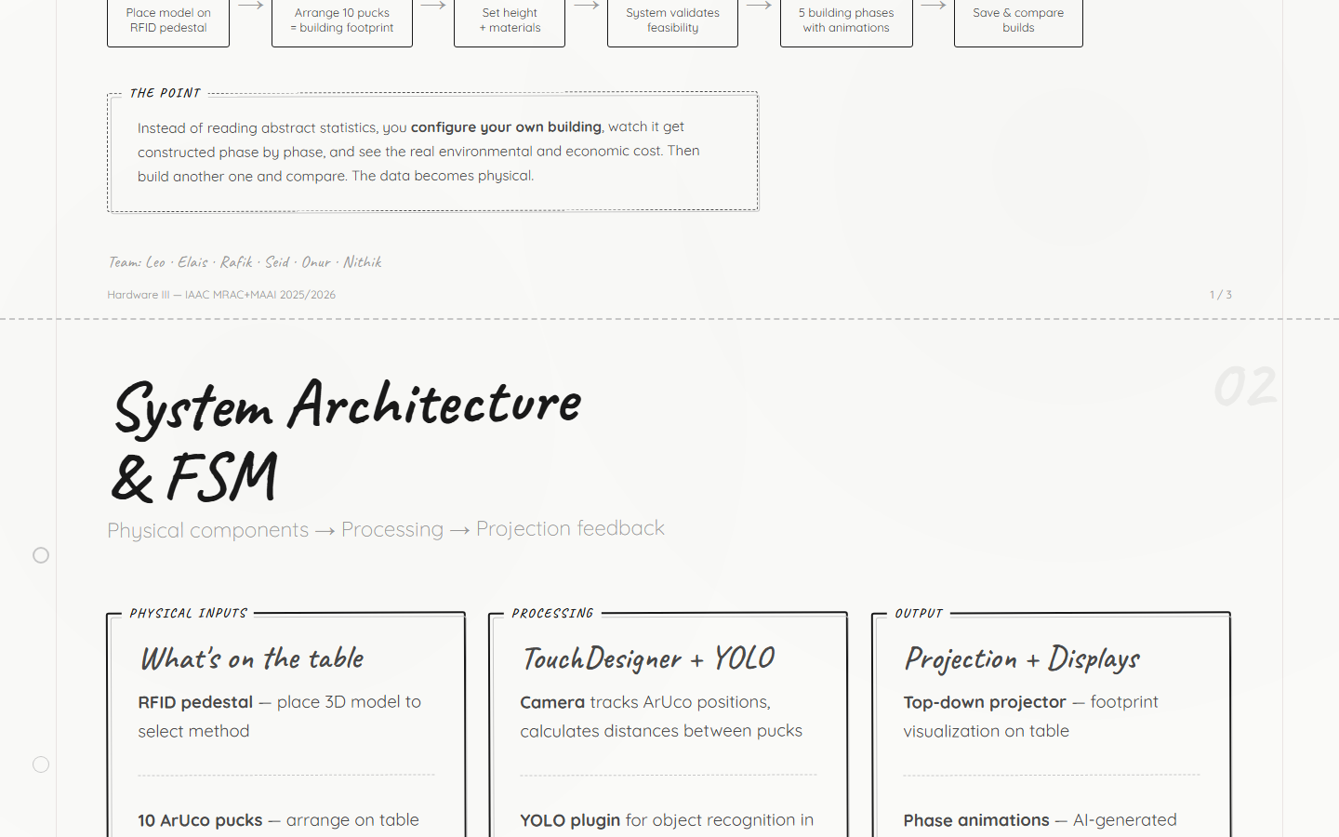
deliverables/screenshot_slide2.png
