Leonardboeker/Hardware_III/deliverables/screenshot_slide3.png

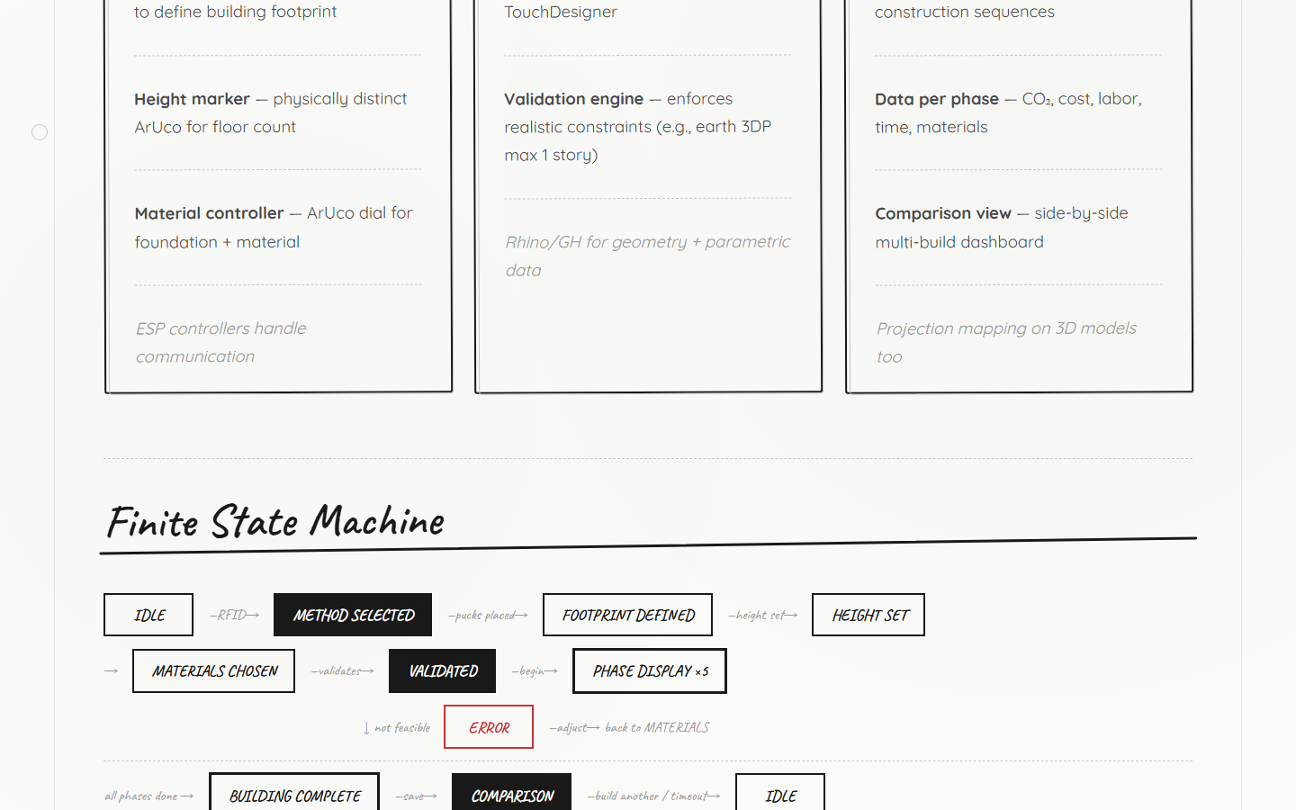
deliverables/screenshot_slide3.png
