Leonardboeker/Hardware_III/cad/aruco-markers/aruco_id11_material.png

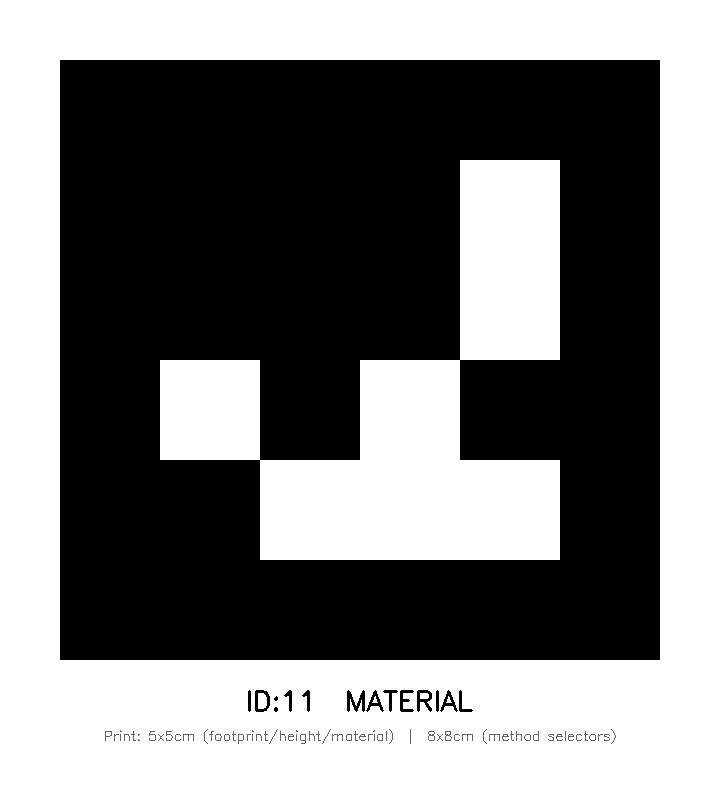
cad/aruco-markers/aruco_id11_material.png
