Leonardboeker/Hardware_III/cad/aruco-markers/aruco_id21_method_3d_print.png

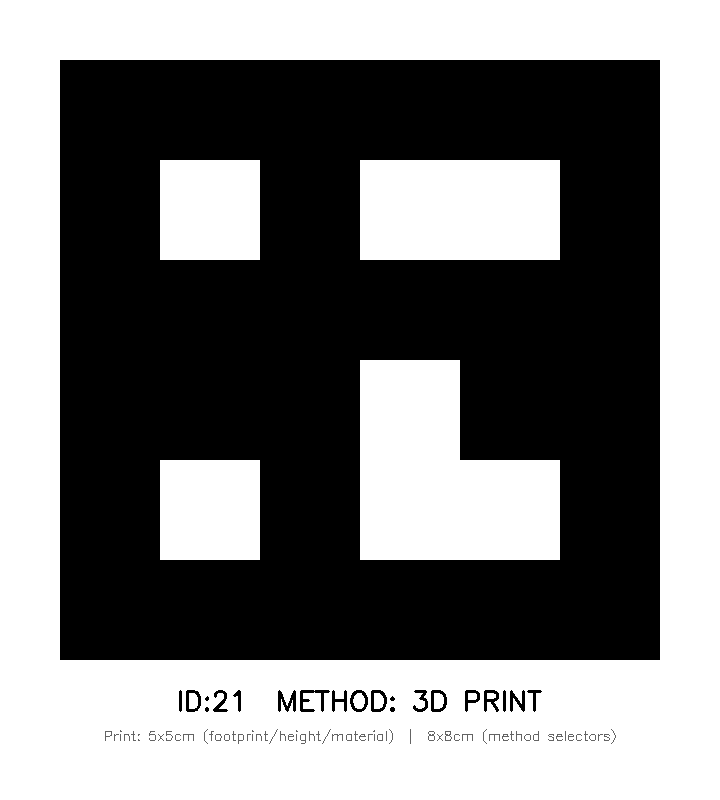
cad/aruco-markers/aruco_id21_method_3d_print.png
